andriy-bilynskyy/HF-BPF/HF-BPF.asc

C1: cap; 2.2n
C2: cap; 1.5n
C3: cap; 1.5n
C4: cap; 2.2n
C5: cap; 33n
C6: cap; 10n
C7: cap; 10n
C8: cap; 82p
C9: cap; 180p
C10: cap; 150p
C11: cap; 68p
C12: cap; 4.7p
C13: cap; 22p
C14: cap; 15pF
L1: ind; 3.2µ
L2: ind; 2.5µ
L3: ind; 3.6µ
L4: ind; 370n
L5: ind; 380n
L6: ind; 360n
R1: res; 50
V1: voltage; AC 1.; Rser=50
Named nets: 0
.ac lin 10000 0.1Meg 150Meg
HF BPF 1.8MHz - 30MHz
**L1:
Core: Amidon T68-1 (17.5x9.40x4.83 Al=115)
Wire diameter d: 0.6 mm
Number of turns of the coil N = 16.7
 
**L2:
Core: Amidon T68-1 (17.5x9.40x4.83 Al=115)
Wire diameter d: 0.6 mm
Number of turns of the coil N = 14.7
 
**L3:
Core: Amidon T68-1 (17.5x9.40x4.83 Al=115)
Wire diameter d: 0.6 mm
Number of turns of the coil N = 17.7
 
**L4:
Former diameter D: 5 mm
Wire diameter d: 0.6 mm
Winding pitch p: 0.77 mm
Number of turns of the coil N = 12
Length of winding l = 9.883 mm
 
**L5:
Former diameter D: 5 mm
Wire diameter d: 0.6 mm
Winding pitch p: 0.75 mm
Number of turns of the coil N = 12
Length of winding l = 9.688 mm
 
**L6:
Former diameter D: 5 mm
Wire diameter d: 0.6 mm
Winding pitch p: 0.8 mm
Number of turns of the coil N = 12
Length of winding l = 10.239 mm
